AlexanderSaal/Analog_Computer_Polar_Coordinate_Transformator/Coordinate_Transformer/schematic/PCB-1.png

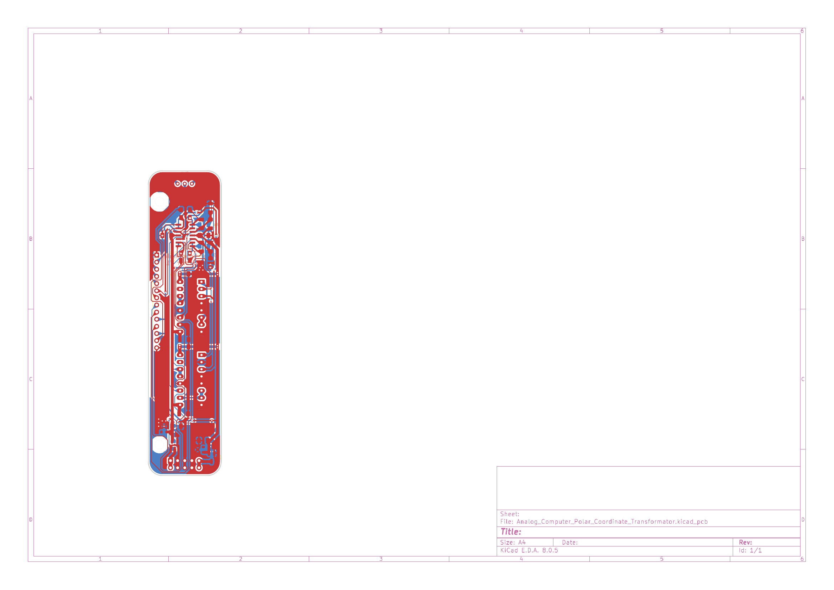
Coordinate_Transformer/schematic/PCB-1.png
